ucb-ee290c/BearlyML-PCB/assets/bearlyml_processed.jpg

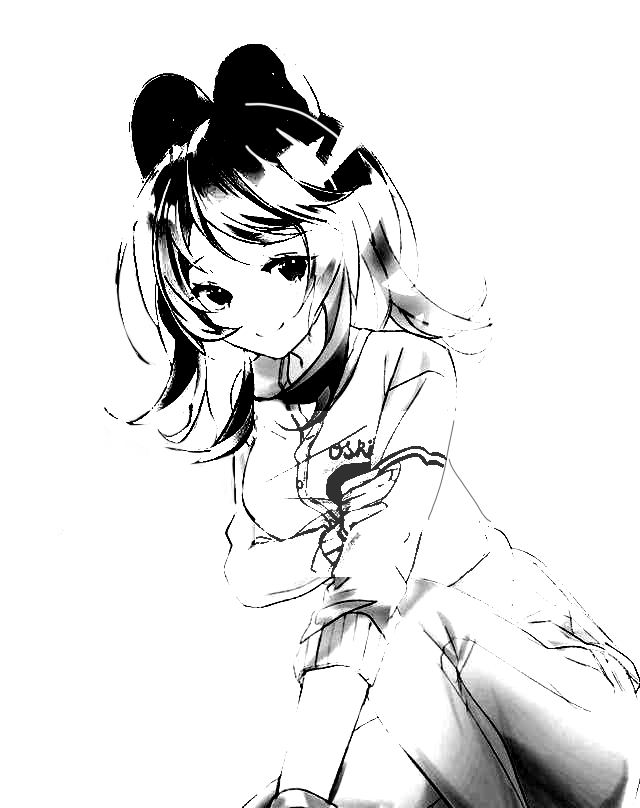
assets/bearlyml_processed.jpg
