ucb-ee290c/BearlyML-PCB/assets/slice.png

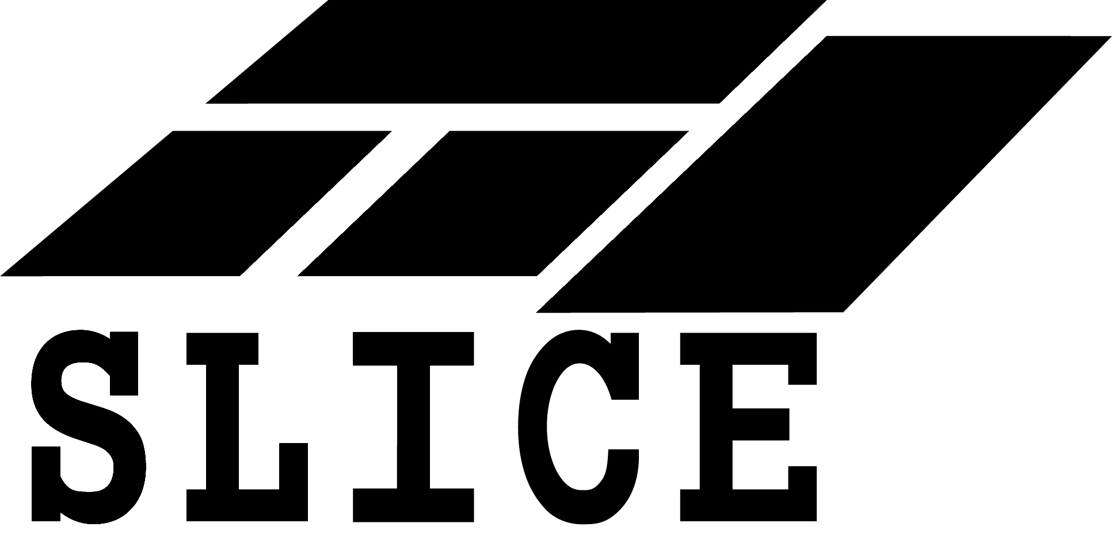
assets/slice.png
